Kinznice/4S-SIF/Images/c2.jpg

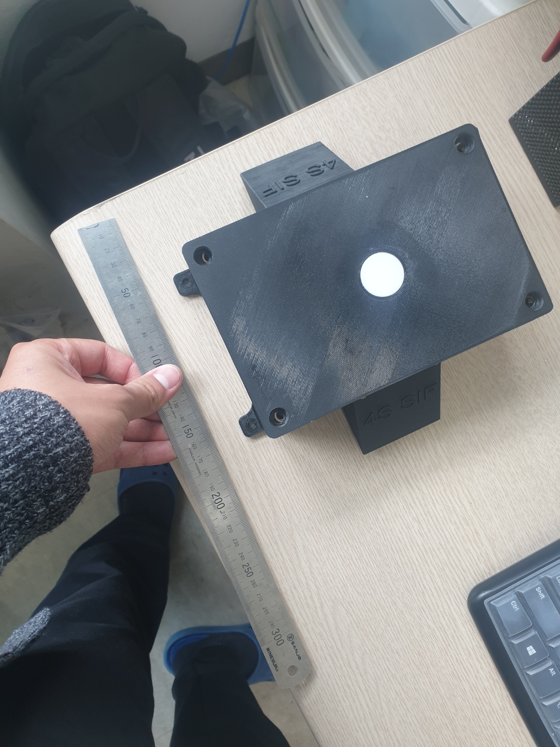
Images/c2.jpg
