Kinznice/4S-SIF/Images/c3.jpg

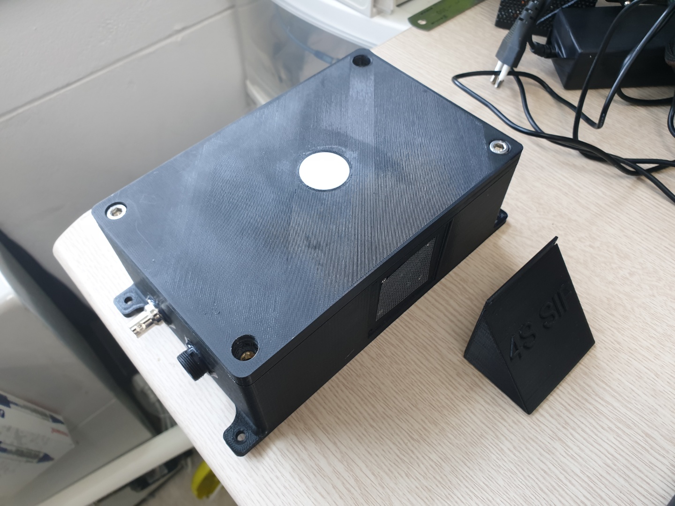
Images/c3.jpg
