Kinznice/4S-SIF/Images/c5.jpg

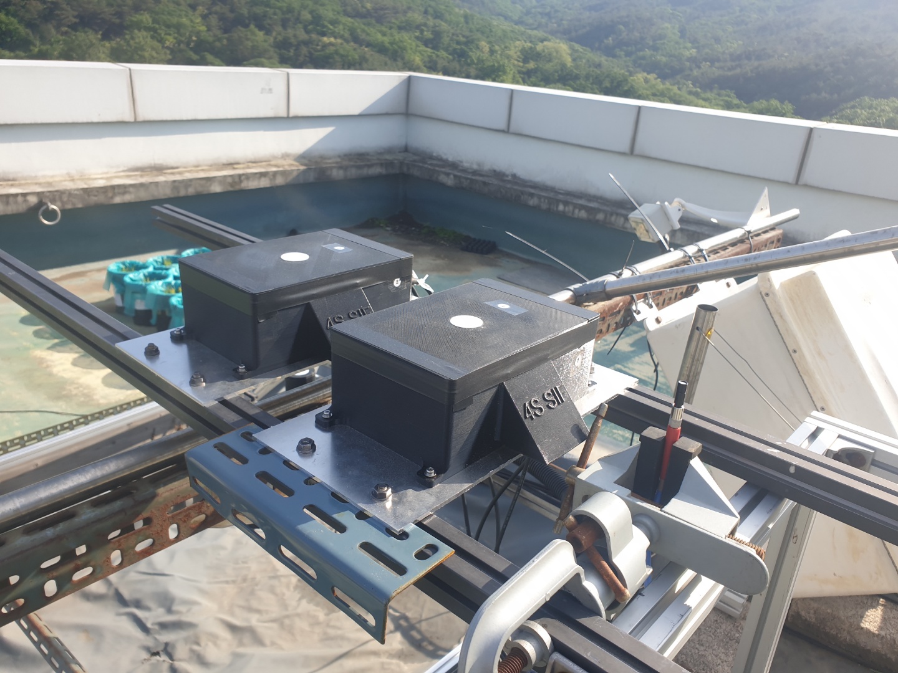
Images/c5.jpg
