Kinznice/4S-SIF/Images/c7.jpg

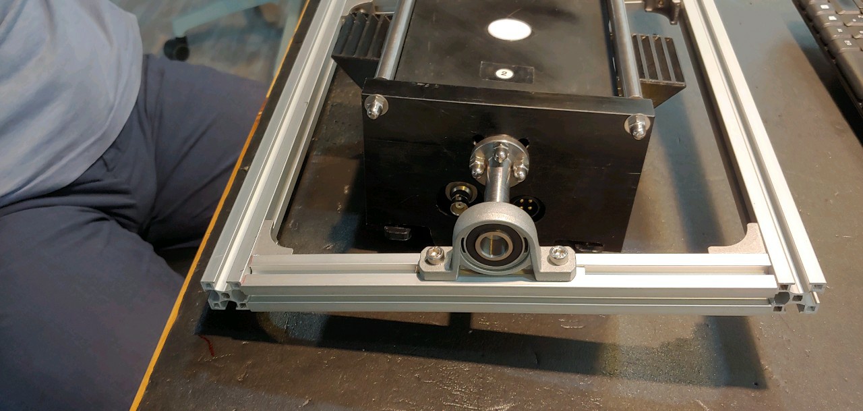
Images/c7.jpg
