Kinznice/4S-SIF/Images/c9.jpg

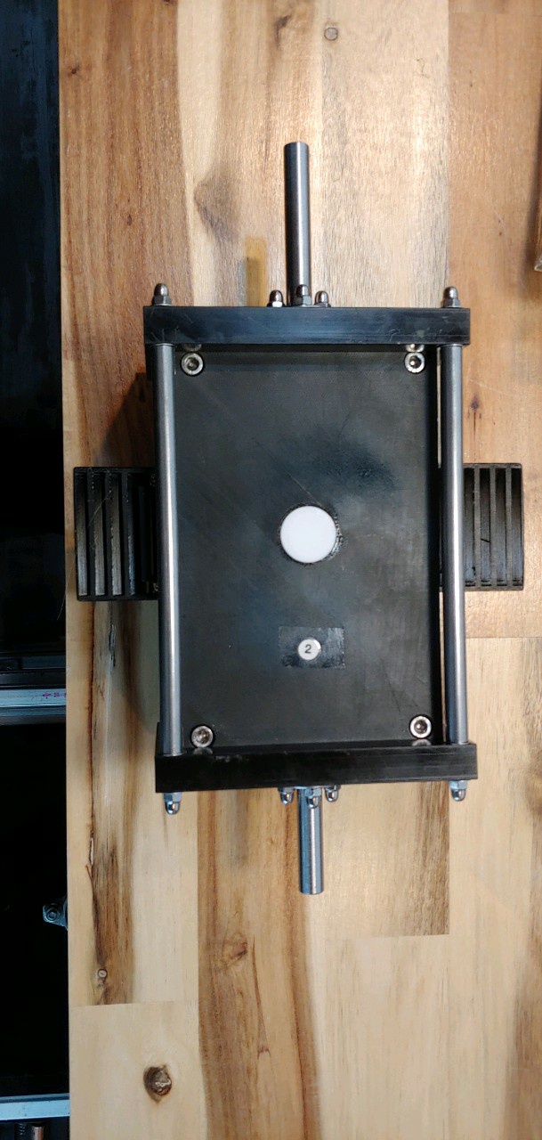
Images/c9.jpg
